brianssparetime/bronica_kiev_prism_plate/kiev_plate_scan/kiev prism plate scan.jpg

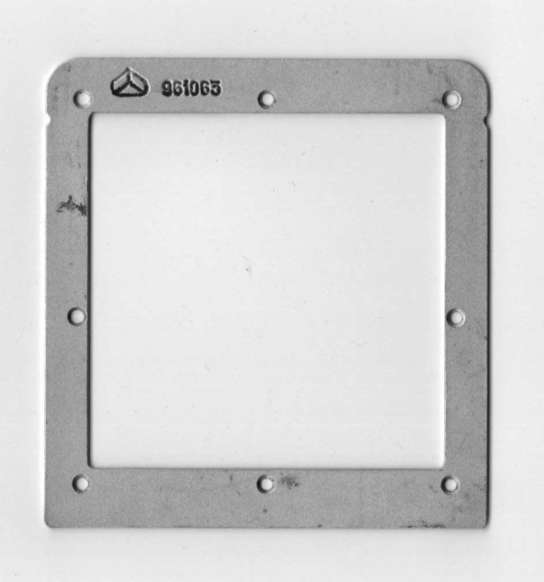
kiev_plate_scan/kiev prism plate scan.jpg
